JarofMolasses/macroscope/CAD archive/Probe.SLDPRT

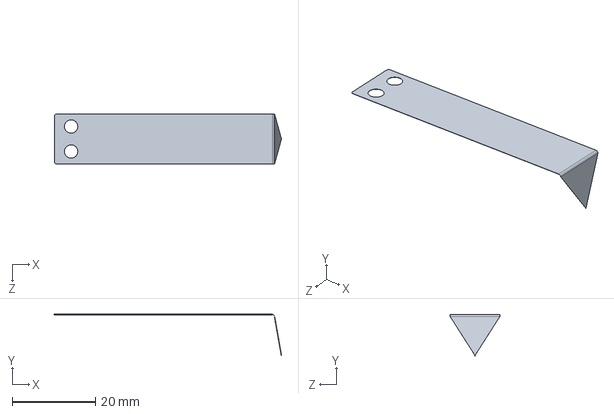
[picture p15: CAD file, 2025-08-22, an earlier design]
CAD archive/Probe.SLDPRT
54.5 x 9.86 x 12.0 mm
