JarofMolasses/macroscope/CAD archive/Corner_Bracket_423.SLDPRT

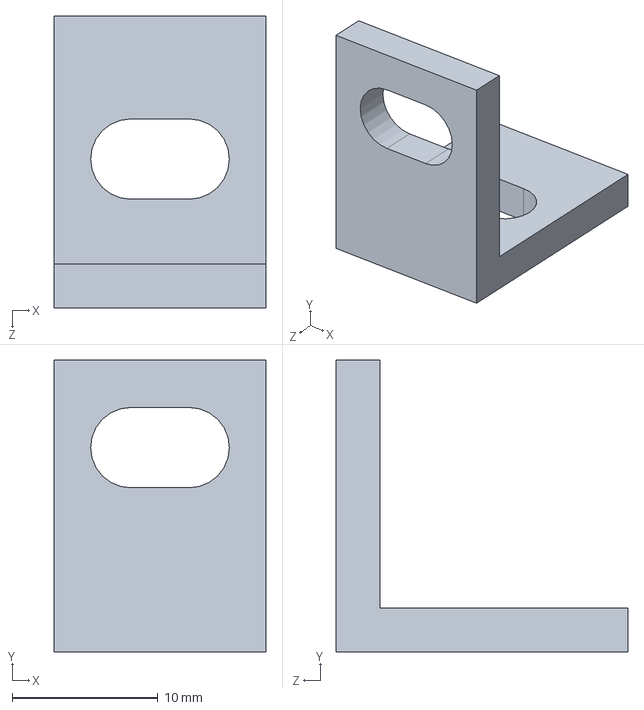
[picture p16: CAD file, 2025-08-22, an earlier design]
CAD archive/Corner_Bracket_423.SLDPRT
14.5 x 20.0 x 20.0 mm
