JarofMolasses/macroscope/CAD archive/Actuator_movable.SLDASM

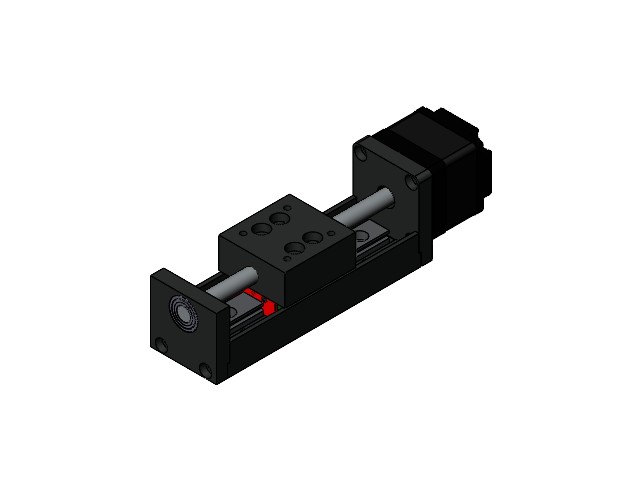
[picture p17: CAD file, 2025-08-22, an earlier design]
CAD archive/Actuator_movable.SLDASM
Base
Wall_Back
Wall_Front
Actuator_MGN9
Actuator_MGN9C
Carriage
Nema11
